mixographer/Attiny84_chess_clock/Images/board.JPG

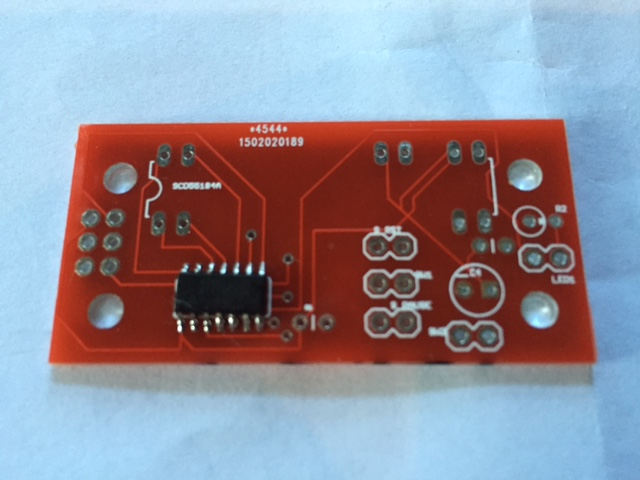
Images/board.JPG
