mixographer/Attiny84_chess_clock/Images/proto1.JPG

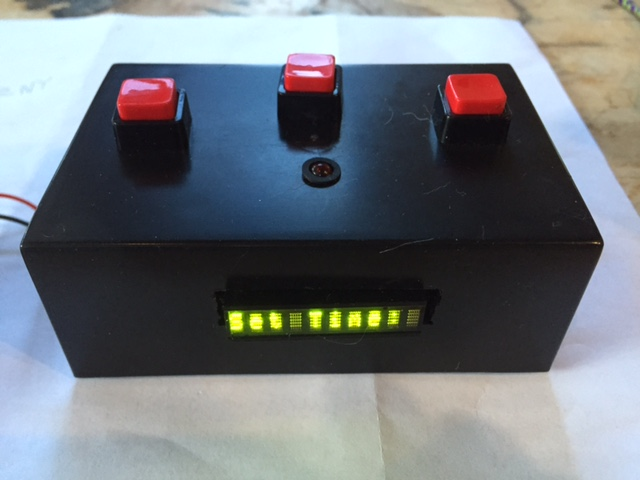
Images/proto1.JPG
